SimpleMethod/Horizon/IoT server/Website/render_black_transparent.png

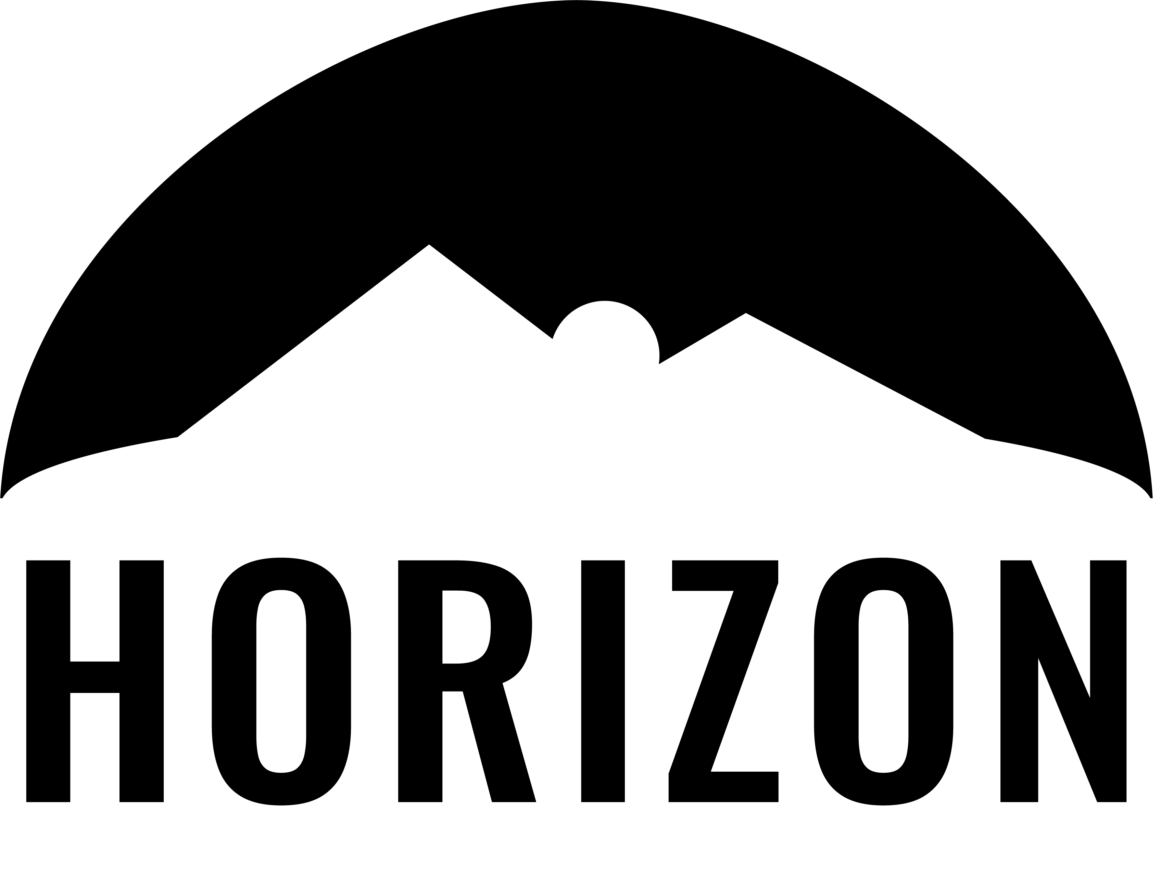
IoT server/Website/render_black_transparent.png
