SimpleMethod/Horizon/Base station/Mainboard pcb files/Wiring diagram PNG files/Wiring diagram/BaseStation_WiringDiagram.png

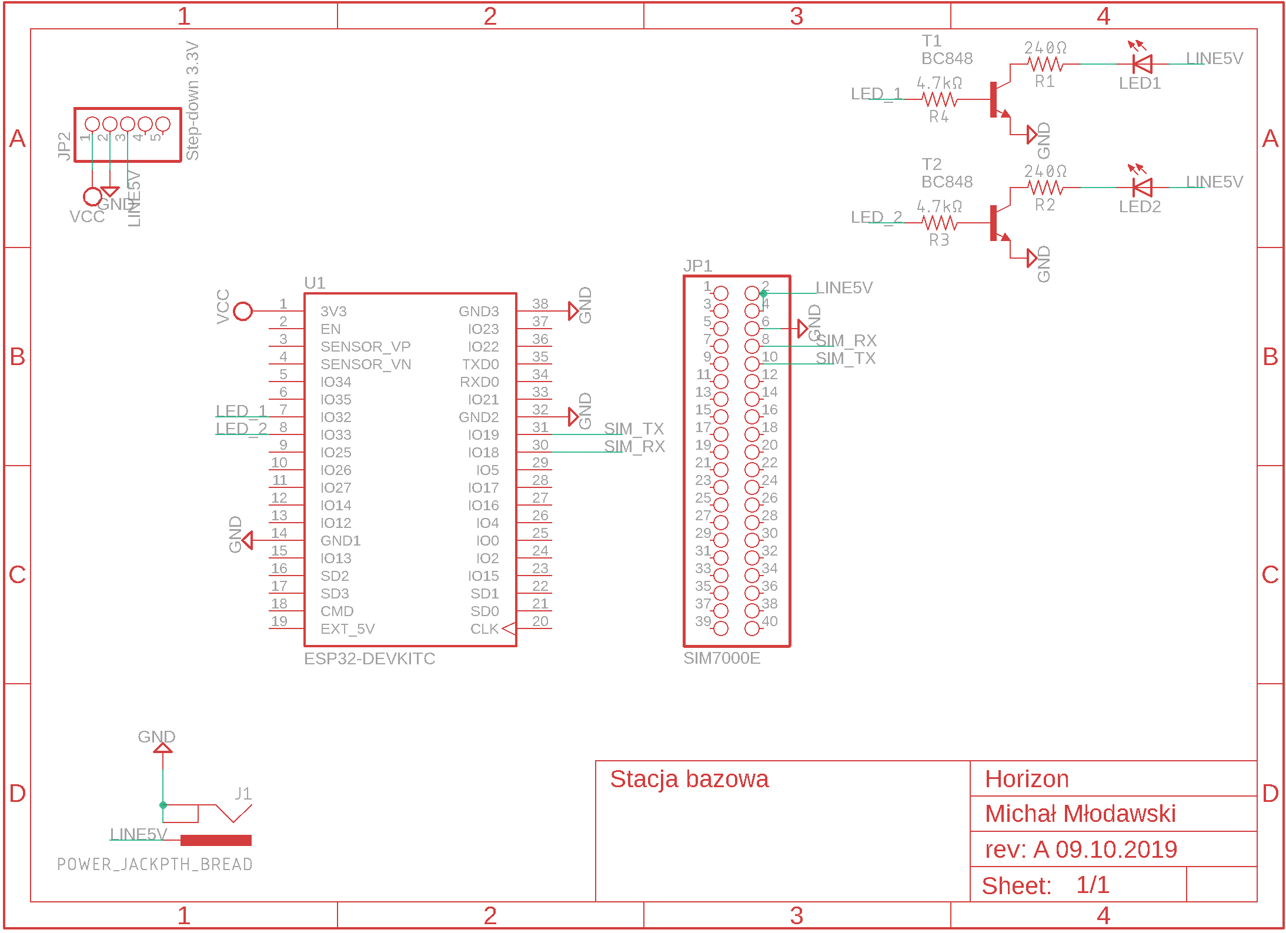
Base station/Mainboard pcb files/Wiring diagram PNG files/Wiring diagram/BaseStation_WiringDiagram.png
