SimpleMethod/Horizon/Client station/Source code/STM32 Controller/Src/main.c

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

/* Includes ------------------------------------------------------------------*/
#include "main.h"

/* USER CODE BEGIN Includes */
#include "sds011.h"


#include <stdio.h>
#include <stdarg.h>
#include <string.h>
/* USER CODE END Includes */

/* USER CODE BEGIN PTD */
#define BME280
/* USER CODE END PTD */

ADC_HandleTypeDef hadc;

I2C_HandleTypeDef hi2c1;
DMA_HandleTypeDef hdma_i2c1_rx;
DMA_HandleTypeDef hdma_i2c1_tx;

TIM_HandleTypeDef htim3;

UART_HandleTypeDef huart1;
UART_HandleTypeDef huart2;

/* USER CODE BEGIN PV */
SDS sds;

uint8_t data[50];
uint16_t size = 0;


uint8_t pm2_5,pm10;


uint32_t ADC_raw, Vdd;
/* USER CODE END PV */

void SystemClock_Config(void);
static void MX_GPIO_Init(void);
static void MX_DMA_Init(void);
static void MX_ADC_Init(void);
static void MX_USART1_UART_Init(void);
static void MX_USART2_UART_Init(void);
static void MX_TIM3_Init(void);
static void MX_I2C1_Init(void);
/* USER CODE BEGIN PFP */
void HAL_TIM_PeriodElapsedCallback(TIM_HandleTypeDef *htim){
 if(htim->Instance == TIM3){
	 pm2_5 = sdsGetPm2_5(&sds); pm10= sdsGetPm10(&sds);
 }
}
/* USER CODE END PFP */

/* USER CODE BEGIN 0 */
void vprint(const char *fmt, va_list argp) {
	char string[200];
	if (0 < vsprintf(string, fmt, argp)) // build string
			{
		HAL_UART_Transmit(&huart1, (uint8_t*) string, strlen(string), 0xffffff); // send message via UART
	}
}

void my_printf(const char *fmt, ...) // custom printf() function
{
	va_list argp;
	va_start(argp, fmt);
	vprint(fmt, argp);
	va_end(argp);
}

void HAL_ADC_ConvCpltCallback(ADC_HandleTypeDef* hadc)
{
  if (__HAL_ADC_GET_FLAG(hadc, ADC_FLAG_EOC))
    {
    ADC_raw = HAL_ADC_GetValue(hadc);
    }
}
/* USER CODE END 0 */

/**
  * @brief  The application entry point.
  * @retval int
  */
int main(void)
{
  

  /* MCU Configuration--------------------------------------------------------*/

  /* Reset of all peripherals, Initializes the Flash interface and the Systick. */
  HAL_Init();

  /* Configure the system clock */
  SystemClock_Config();

  /* Initialize all configured peripherals */
  MX_GPIO_Init();
  MX_DMA_Init();
  MX_ADC_Init();
  MX_USART1_UART_Init();
  MX_USART2_UART_Init();
  MX_TIM3_Init();
  MX_I2C1_Init();
  /* USER CODE BEGIN 2 */
  HAL_TIM_Base_Start_IT(&htim3);
	sdsInit(&sds, &huart2);
	sdsWorkingMode(&sds);
  /* USER CODE END 2 */

  /* Infinite loop */
  /* USER CODE BEGIN WHILE */
  while (1)
  {
    /* USER CODE END WHILE */

    /* USER CODE BEGIN 3 */

	  while (1)
	   {
	     /* USER CODE END WHILE */

	     /* USER CODE BEGIN 3 */
	 	  if (__HAL_UART_GET_FLAG(&huart1, UART_FLAG_RXNE) == SET)
	 	  {
	 	  uint8_t value;
	 	  HAL_UART_Receive(&huart1, &value, 1, 100);
	 	  switch (value) {
			case 50:
				 my_printf("%d\n\r",  pm2_5);
				break;
			case 51:
				my_printf("%d\n\r",pm10);
				break;
			case 52:
				sdsWorkingMode(&sds);
				break;
			case 53:
				sdsSleepMode(&sds);
				break;
			case 54:
				my_printf("CONNECTION TEST\n\r");
					break;
			case 55:
		 		 my_printf("RAW DATA: %d %d\n\r",  pm2_5, pm10);
					break;
			default:
				break;
		}
	 	  }
	   }
  }
  /* USER CODE END 3 */
}

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
/* USER CODE BEGIN 4 */
void HAL_UART_RxCpltCallback(UART_HandleTypeDef *huart)
{
sds_uart_RxCpltCallback(&sds,huart);
}
/* USER CODE END 4 */
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
